lessthan00/current-to-voltage-loop/current-to-voltage-loop.asc

R1: res; 1000
Ra: res; 966
Rb: res; 7161
Rc: res; 39.9
Rd: res; 10
Re: res; 50
Rload: res; 250
U1: ADA4622
U3: 2SC2873
V1: voltage; 5
V2: voltage; 36
Va: voltage; 0.2
Named nets: 0, loop+, loop-, Vb
.dc Va 0.1 3.2 0.01
.options cshunt=1e-15
